zhongli0226/ESP32_Weather-station/2.Firmware/weather_stationV2.1.0/components/lv_examples/lv_examples/src/lv_ex_style/lv_ex_style_1.png

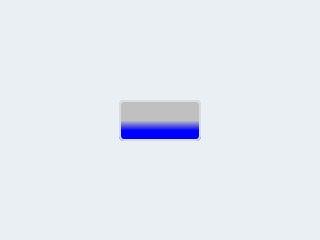
2.Firmware/weather_stationV2.1.0/components/lv_examples/lv_examples/src/lv_ex_style/lv_ex_style_1.png
