zhongli0226/ESP32_Weather-station/2.Firmware/weather_stationV2.1.0/components/lv_examples/lv_examples/src/lv_ex_widgets/lv_ex_spinner/lv_ex_spinner_1.png

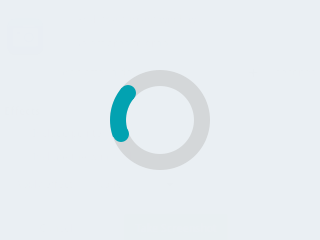
2.Firmware/weather_stationV2.1.0/components/lv_examples/lv_examples/src/lv_ex_widgets/lv_ex_spinner/lv_ex_spinner_1.png
